conyx/boxee.scad/examples/3x4.jpg

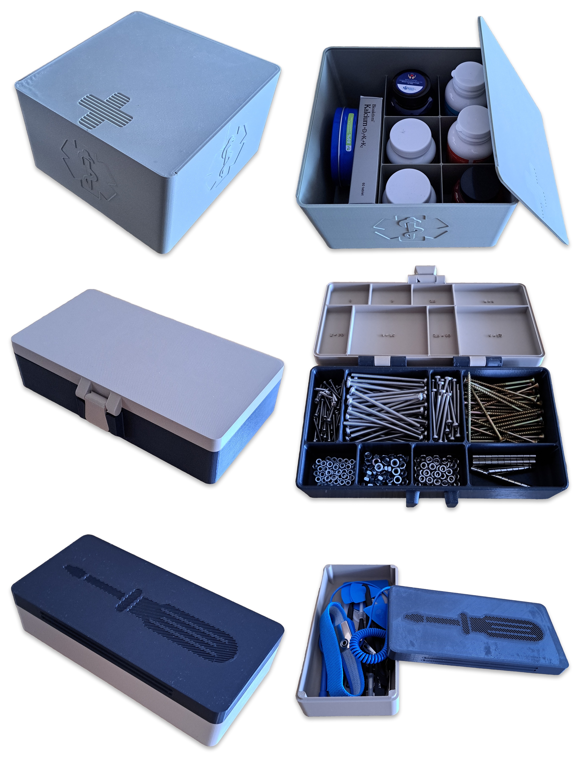
examples/3x4.jpg
