conyx/boxee.scad/examples/medi_box/medi_box_01.jpg

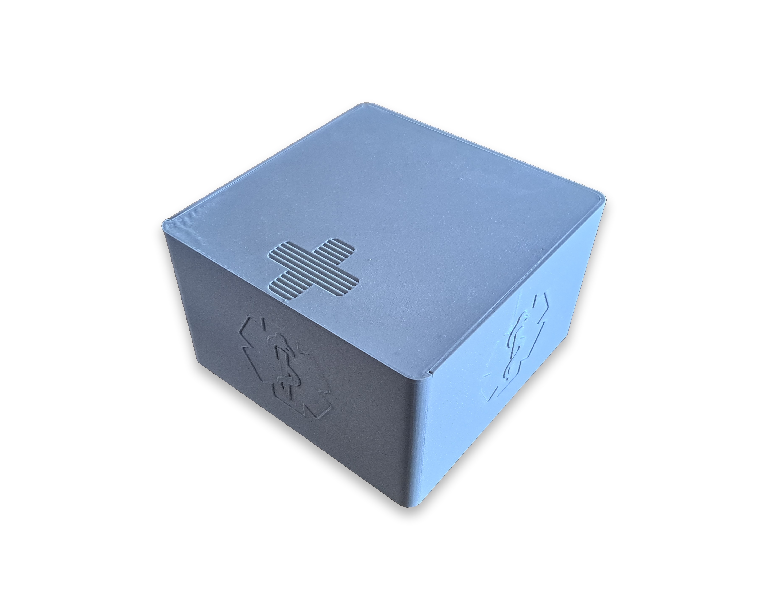
examples/medi_box/medi_box_01.jpg
