conyx/boxee.scad/examples/medi_box/medi_box_02.jpg

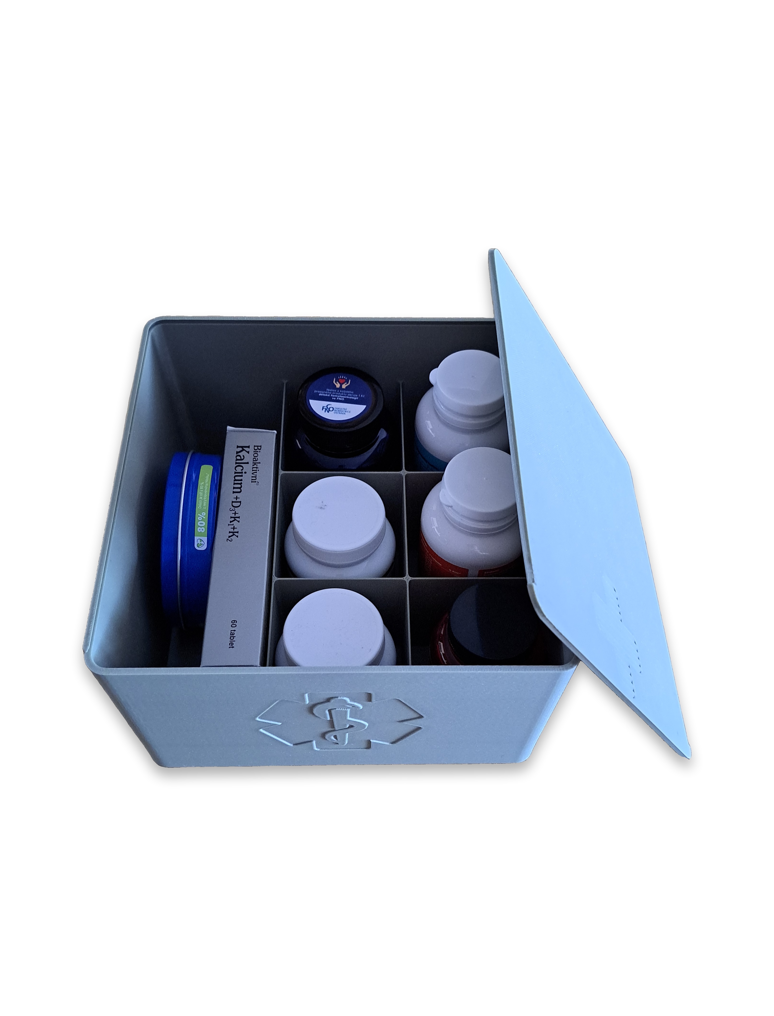
examples/medi_box/medi_box_02.jpg
