conyx/boxee.scad/examples/tool_box/tool_box_01.jpg

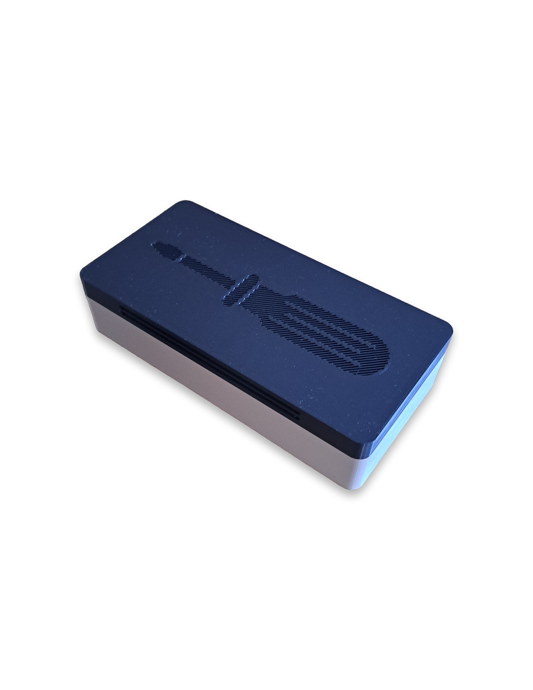
examples/tool_box/tool_box_01.jpg
