conyx/boxee.scad/examples/tool_box/tool_box_02.jpg

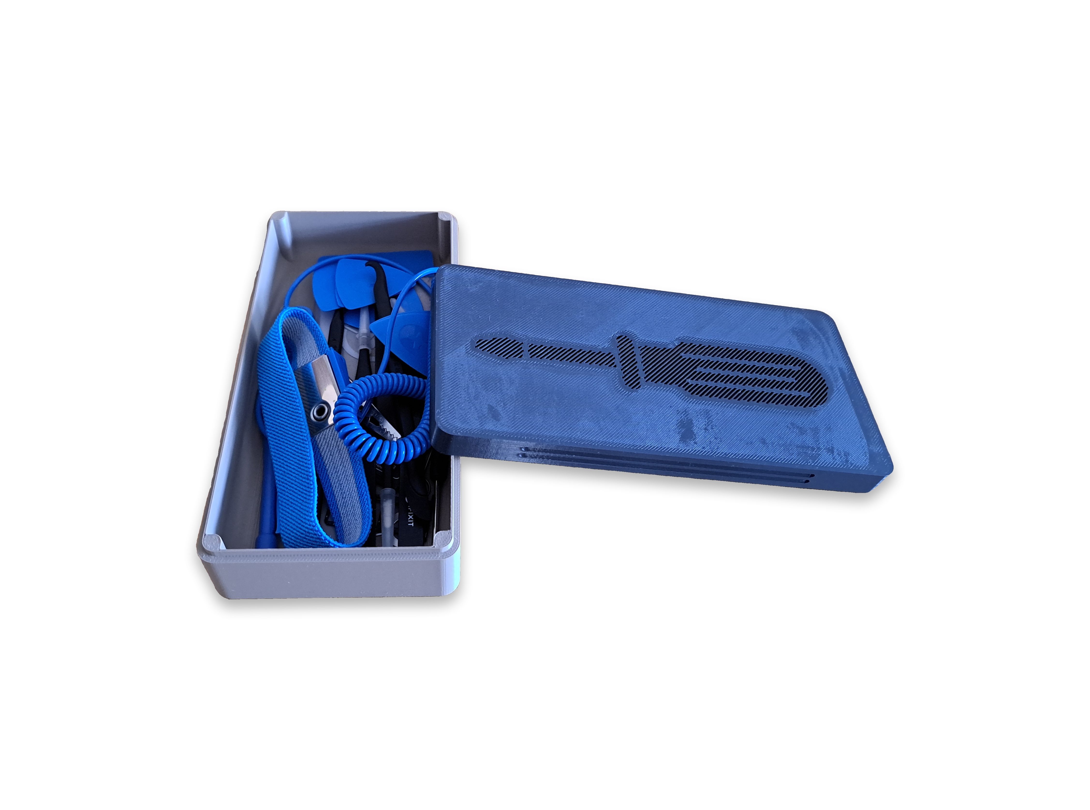
examples/tool_box/tool_box_02.jpg
